SuryaUT/dr-strange-portal/host/ccw_short.png

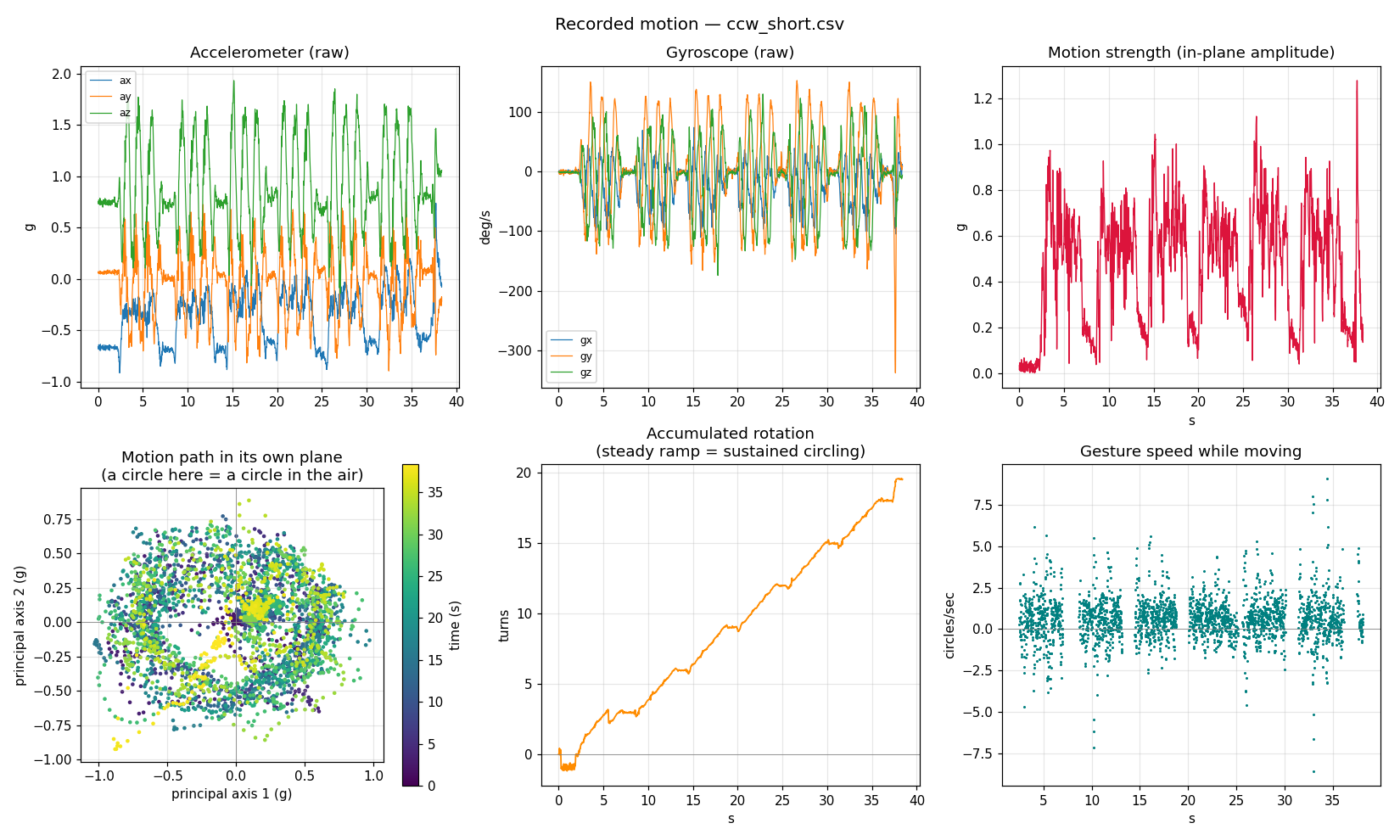
host/ccw_short.png
