SuryaUT/dr-strange-portal/host/cw_raise_then_circle.png

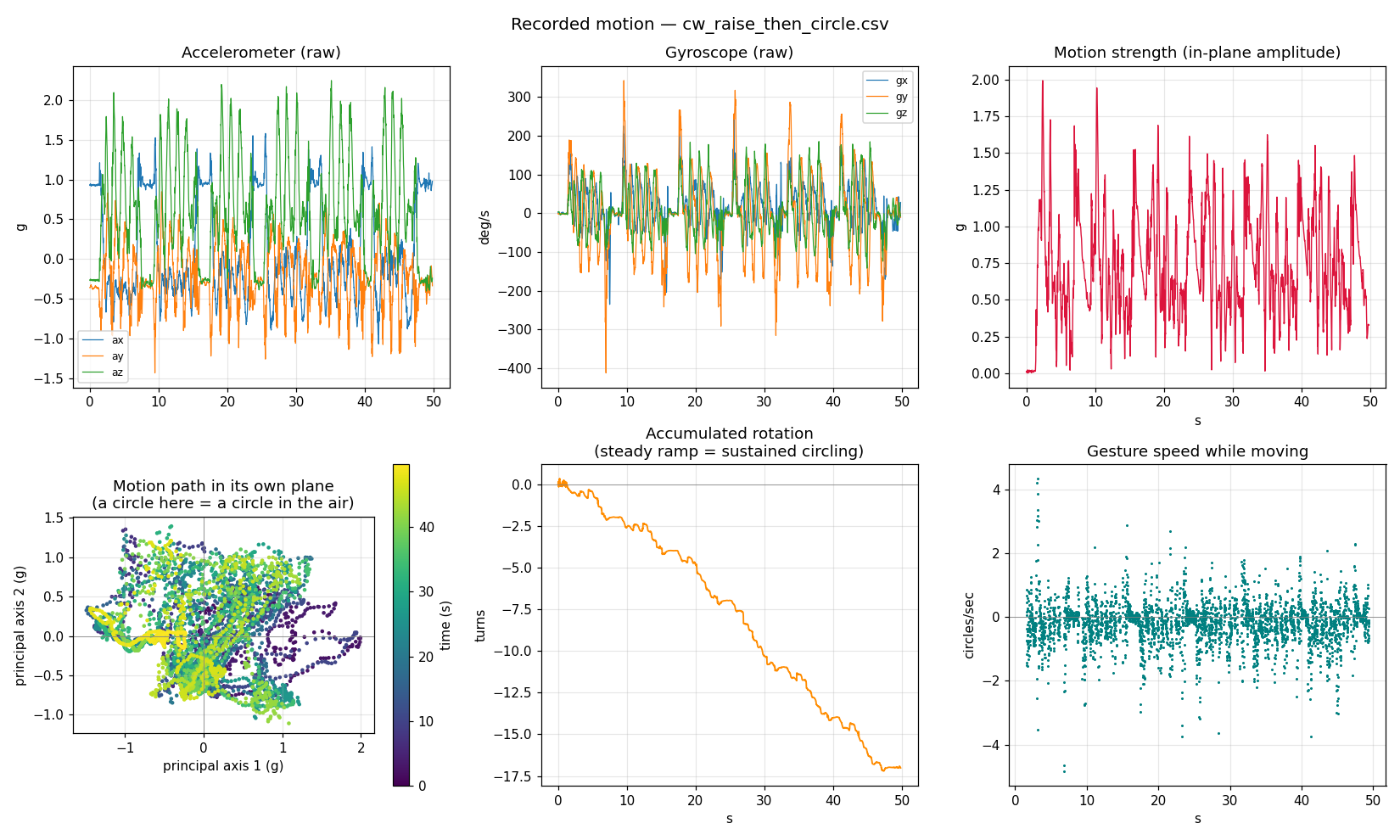
host/cw_raise_then_circle.png
