SuryaUT/dr-strange-portal/host/cw_slow_fast.png

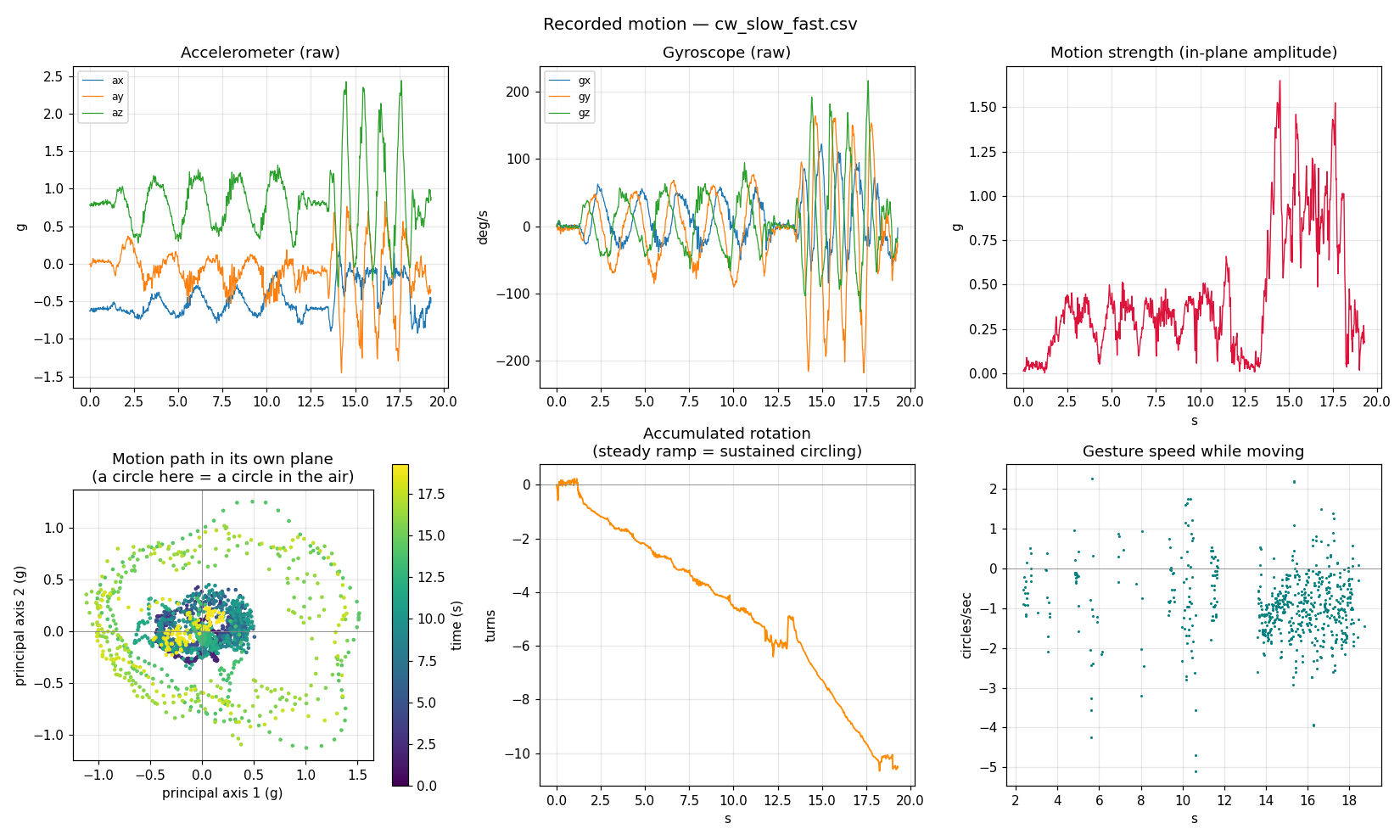
host/cw_slow_fast.png
